plengqui/SportidentTinymesh/docs/RadioUnit1.JPG

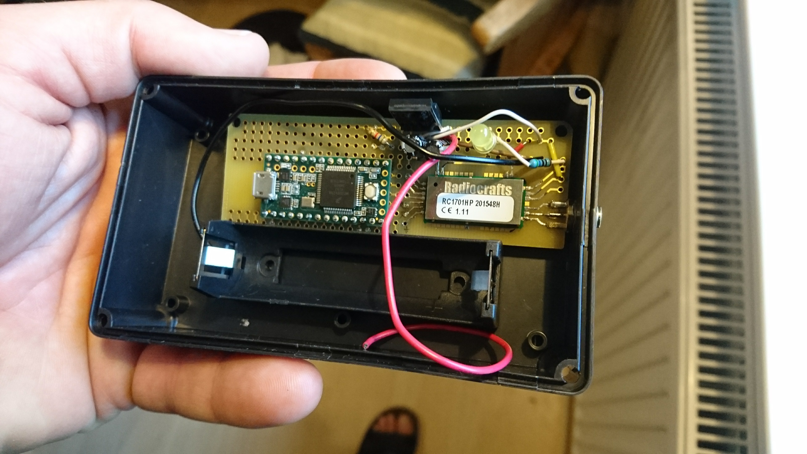
docs/RadioUnit1.JPG
